ell249/RP2040-Debug-Tester/Photos/IMG_8754.jpeg

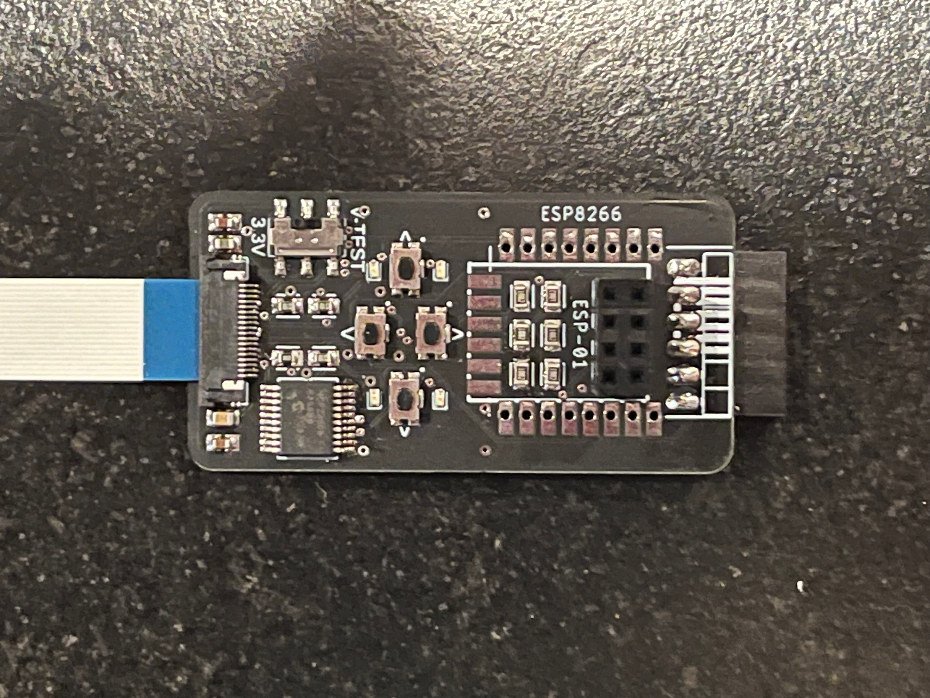
Photos/IMG_8754.jpeg
